eurofurence/ef28-badge/include/FSM.h

#ifndef FSM_H_
#define FSM_H_

// MIT License
//
// Copyright 2024 Eurofurence e.V. 
// 
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
/**
 * @author Honigeintopf
 */

#include <memory>
#include <queue>

#include "FSMEvent.h"
#include "FSMGlobals.h"
#include "FSMState.h"


/**
 * @brief Main finite state machine (FSM)
 */
class FSM {
    
    protected:

        unsigned int tickrate_ms;         //!< Amount of milliseconds this FSM whishes to be handle()'ed
        unsigned int state_last_run;      //!< Timestamp of the last execution of the current states run() method

        std::unique_ptr<FSMState> state;     //!< Current FSM state
        std::queue<FSMEvent> eventqueue;     //!< Queue to store FSMEvents. ATTENTION: THIS IS NOT THREAD SAFE ON ITS OWN!
        std::shared_ptr<FSMGlobals> globals; //!< Global FSM state data

        const char* NVS_NAMESPACE = "effsm";  //!< Namespace under which the FSM stores persisted data in non-volatile storage (NVS)

        /**
         * @brief Retrieves the next FSMEvent from the queue in a non-blocking fashion.
         * 
         * @return Next FSMEvent or FSMEvent::NoOp if no events exist
         */
        FSMEvent dequeueEvent();

    public:

        /**
         * @brief Constructs a new main FSM
         * 
         * @param tickrate_ms Milliseconds this FSM wished to be peroidically handle()'ed after
         */
        FSM(unsigned int tickrate_ms);

        /**
         * @brief Destructs the main FSM. De-initializes all resourecs
         */
        ~FSM();

        /**
         * @brief Resumes the FSM to the last state according to NVS data
         */
        void resume();

        /**
         * @brief Performs a transition to the given next state
         * 
         * @param next The state to transition to.
         */
        void transition(std::unique_ptr<FSMState> next);

        /**
         * @brief Retrieves the tick rate of this FSM
         * 
         * @return Tick rate in milliseconds
         */
        unsigned int getTickRateMs();

        /**
         * @brief Enqueues the given event to be handled during the next cycle
         */
        void queueEvent(FSMEvent event);

        /**
         * @brief Retrieves the number of FSMEvents currently waiting to be processed
         * 
         * @return Number of currently queued FSMEvents
         */
        unsigned int getQueueSize();

        /**
         * @brief Execute a processing cycle. Processes all events that are currently queued.
         */
        void handle();

        /**
         * @brief Executes a processing cycle. Only processees num_events at max. If more
         * events are inside the queue, these are handled in the next processing cycle.
         * 
         * @param num_events Maximum number of events from the queue to process during this cycle
         */
        void handle(unsigned int num_events);

        /**
         * @brief Presists the current globals state of this FSM to the NVS partition
         */
        void persistGlobals();

        /**
         * @brief Loads the globals state from the NVS partition and recovers it into current
         * globals FSM state
         */
        void restoreGlobals();

};

#endif /* FSM_H_ */
